SPARC-Auburn/NASA-RMC-2016/Electronics Hardware/Renders/design 3 early sketch.PNG

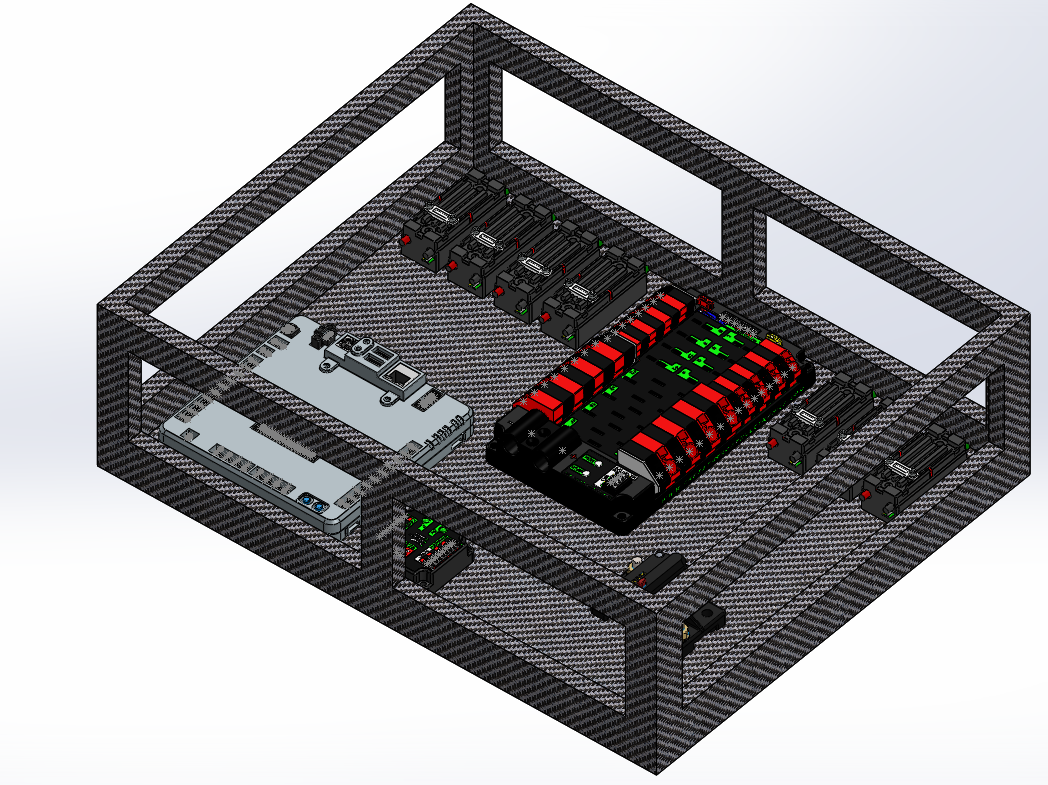
Electronics Hardware/Renders/design 3 early sketch.PNG
