SPARC-Auburn/NASA-RMC-2016/Electronics Hardware/Renders/frame5.PNG

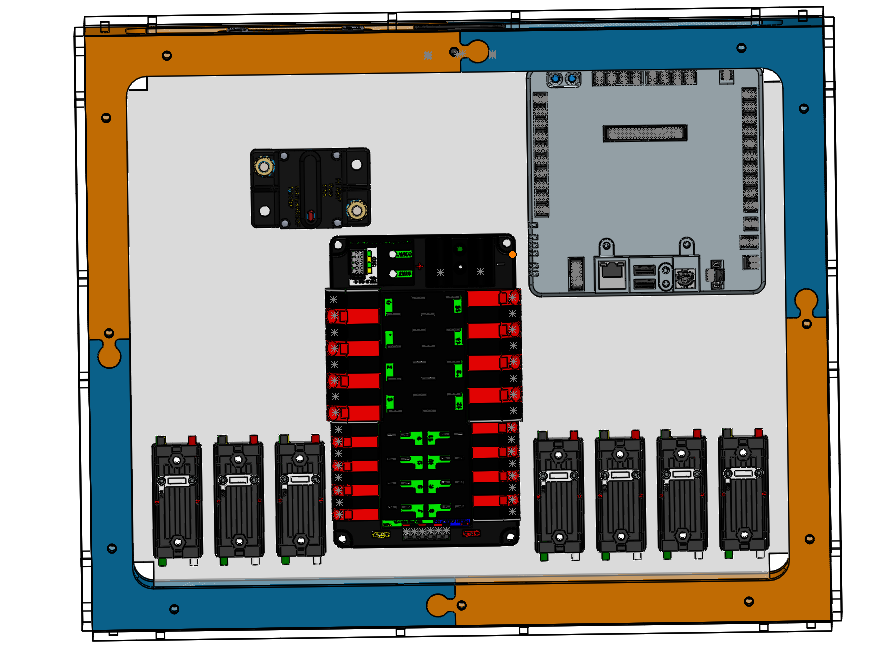
Electronics Hardware/Renders/frame5.PNG
