SPARC-Auburn/NASA-RMC-2016/Electronics Hardware/Renders/snap1.PNG

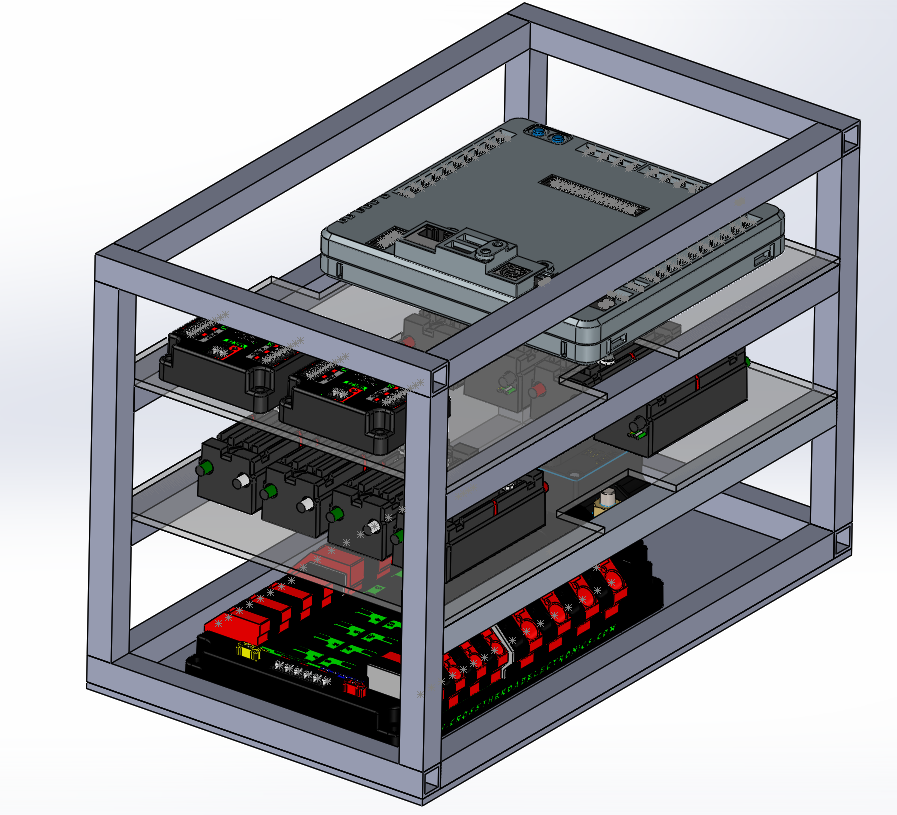
Electronics Hardware/Renders/snap1.PNG
