SPARC-Auburn/NASA-RMC-2016/Electronics Software/Fiducial/spaceclubBlack.png

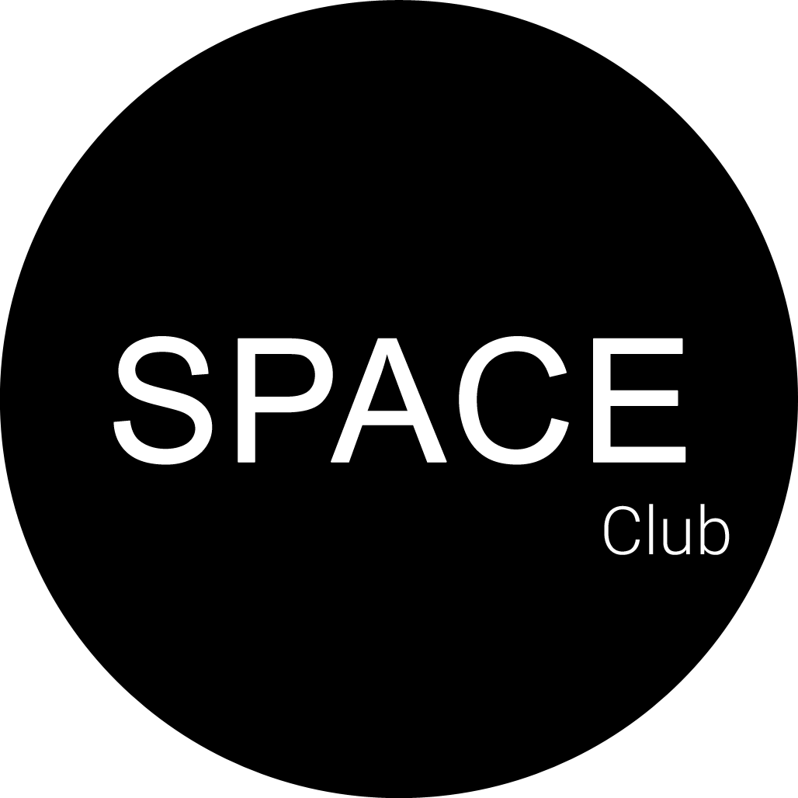
Electronics Software/Fiducial/spaceclubBlack.png
