SPARC-Auburn/NASA-RMC-2016/Electronics Software/Fiducial/sparcABlack.png

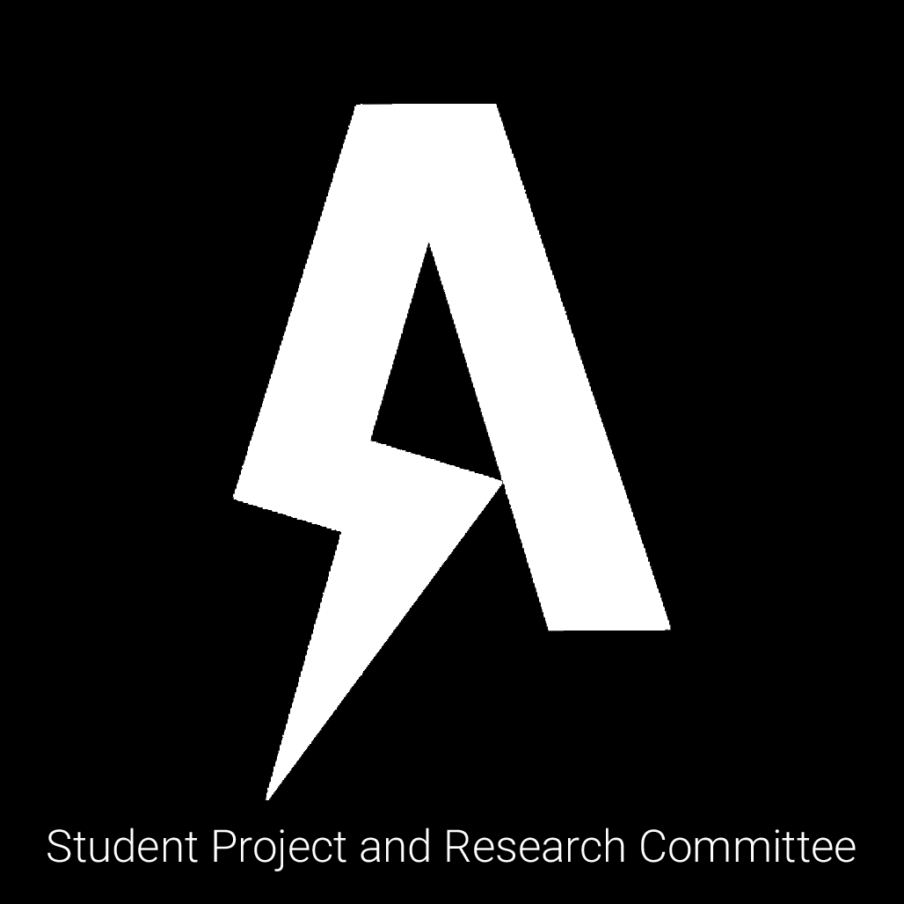
Electronics Software/Fiducial/sparcABlack.png
