SPARC-Auburn/NASA-RMC-2016/Electronics Software/Fiducial/sparcAImpact copy.png

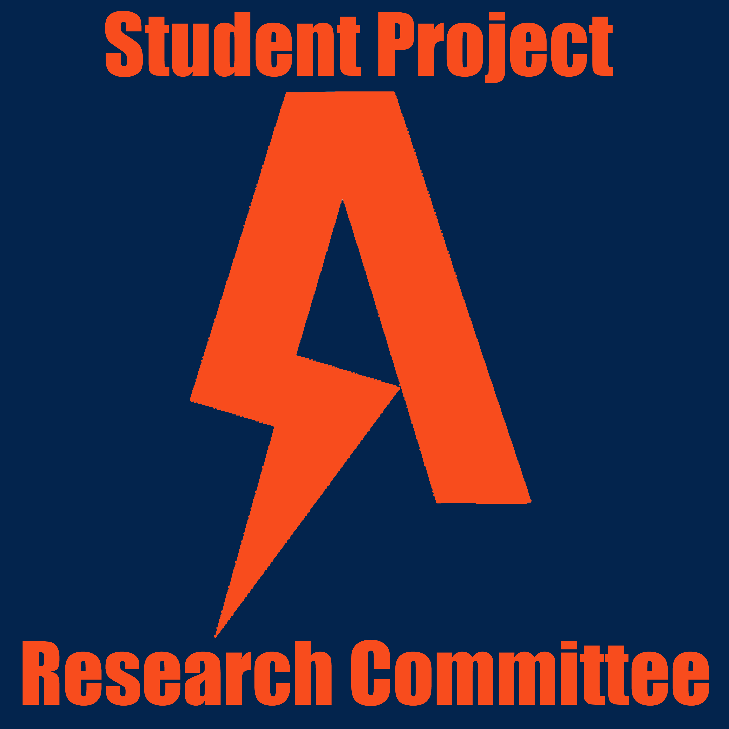
Electronics Software/Fiducial/sparcAImpact copy.png
