SPARC-Auburn/NASA-RMC-2016/Other/T-Shirt/back copy.png

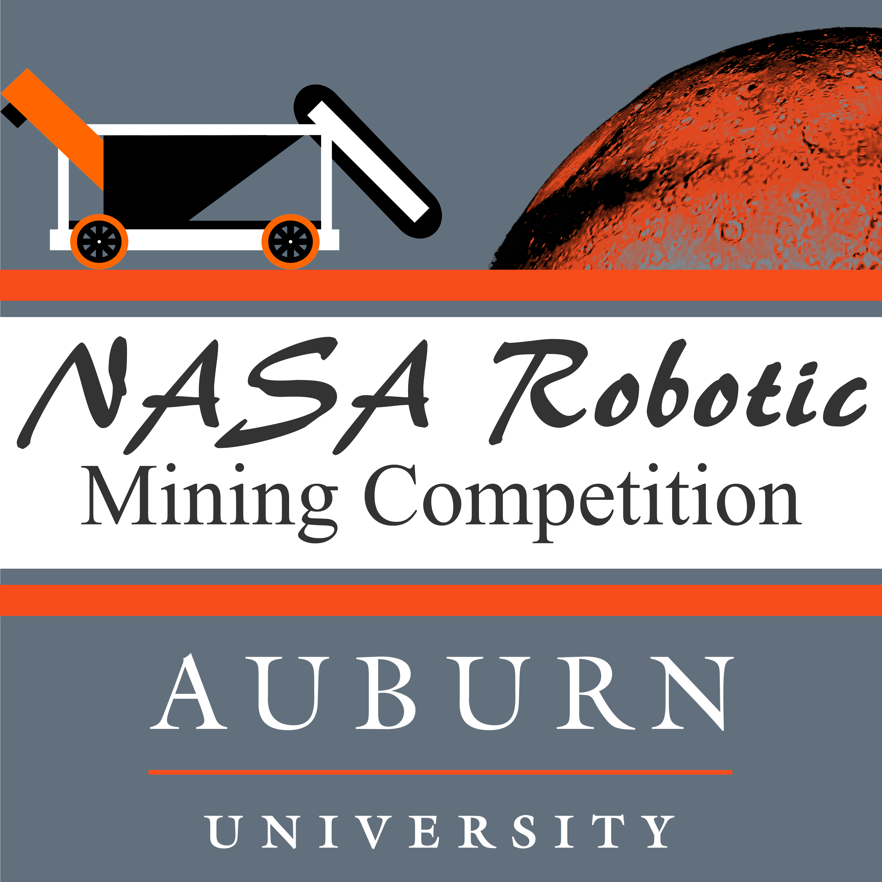
Other/T-Shirt/back copy.png
