SPARC-Auburn/NASA-RMC-2016/Other/T-Shirt/robot.png

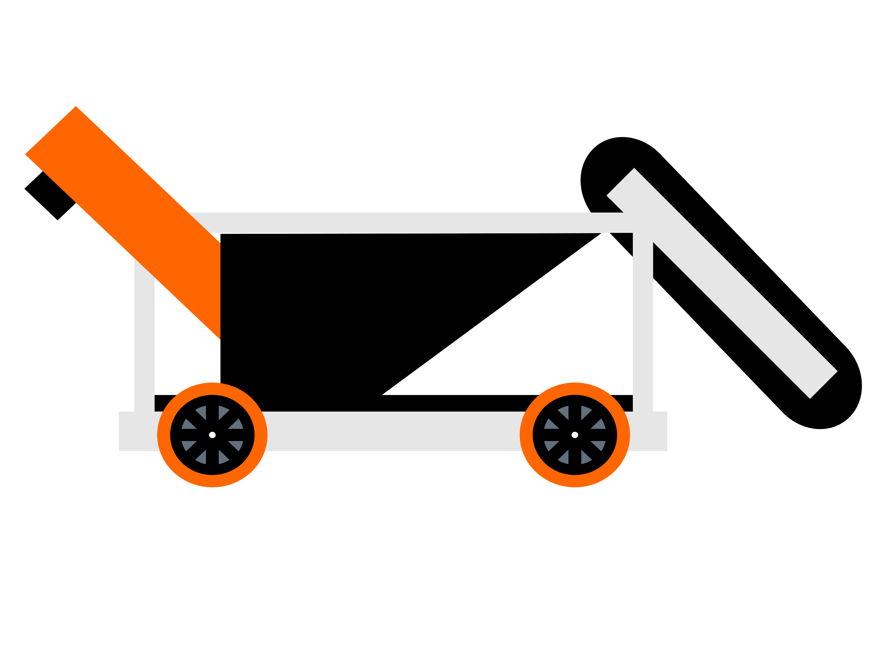
Other/T-Shirt/robot.png
