SPARC-Auburn/NASA-RMC-2016/Electronics Hardware/Final Box CAD/pwrcheck.SLDPRT

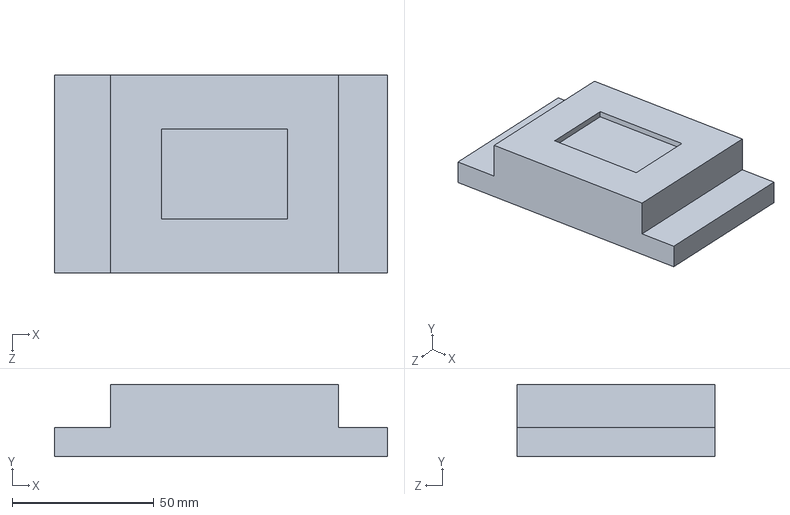
[picture p59: CAD file, 2016-08-08]
Electronics Hardware/Final Box CAD/pwrcheck.SLDPRT
117.5 x 25.4 x 69.8 mm
