SPARC-Auburn/NASA-RMC-2016/Electronics Hardware/Final Box CAD/quarter frame connector.SLDPRT

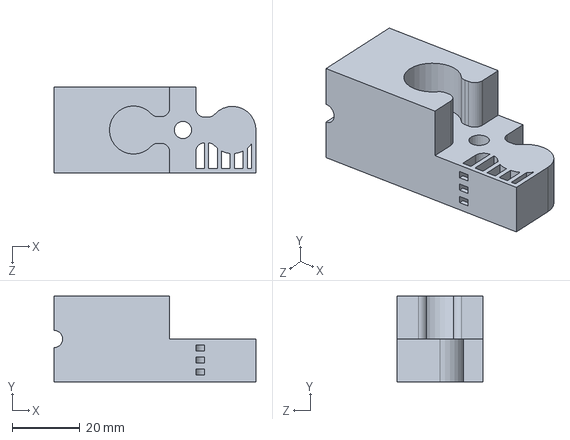
[picture p60: CAD file, 2016-08-08]
Electronics Hardware/Final Box CAD/quarter frame connector.SLDPRT
59.7 x 25.4 x 25.4 mm
