SPARC-Auburn/NASA-RMC-2016/Electronics Hardware/Final Box CAD/Anderson SB50.SLDPRT

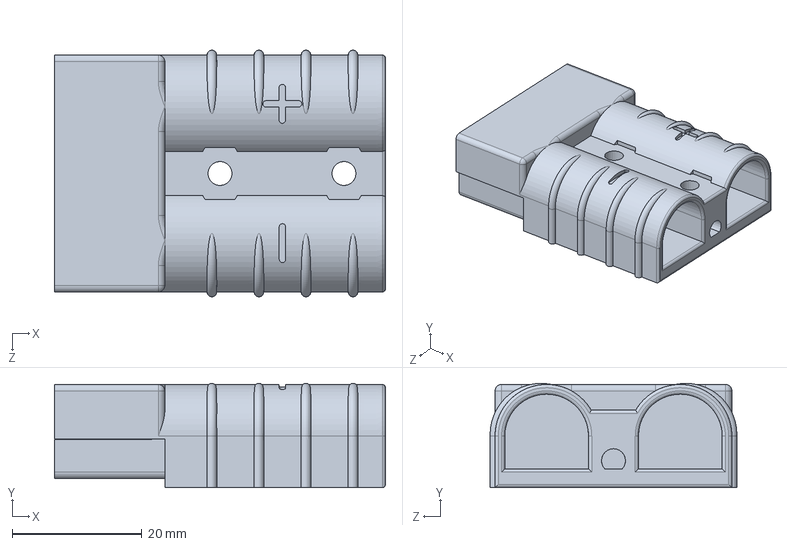
[picture p61: CAD file, 2016-08-08]
Electronics Hardware/Final Box CAD/Anderson SB50.SLDPRT
51.0 x 16.1 x 38.0 mm
