SPARC-Auburn/NASA-RMC-2016/Electronics Hardware/Final Box CAD/powerpole8chassismount.SLDPRT

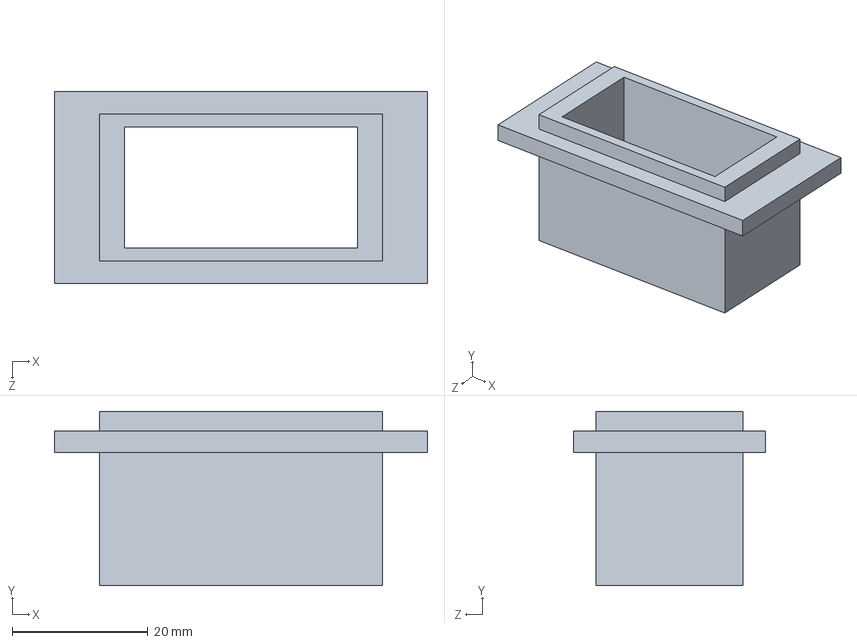
[picture p62: CAD file, 2016-08-08]
Electronics Hardware/Final Box CAD/powerpole8chassismount.SLDPRT
54.9 x 25.7 x 28.2 mm
