SPARC-Auburn/NASA-RMC-2016/Electronics Hardware/Final Box CAD/quarter frame.SLDPRT

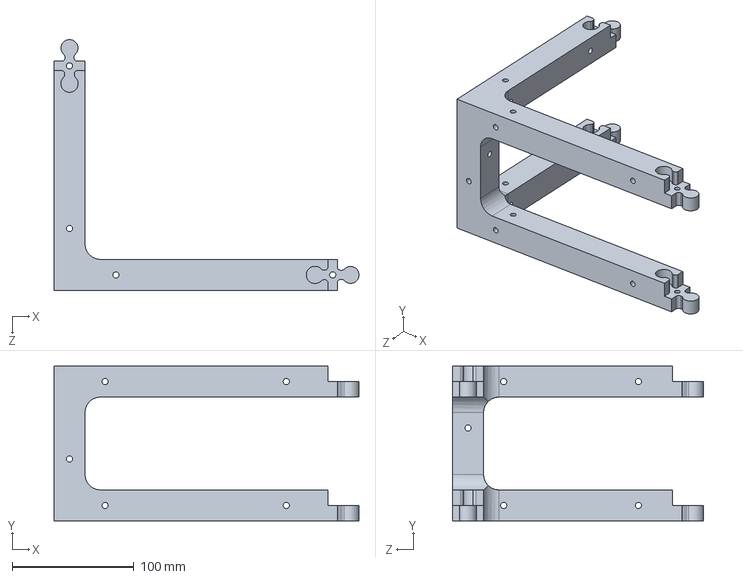
[picture p63: CAD file, 2016-08-08]
Electronics Hardware/Final Box CAD/quarter frame.SLDPRT
250.1 x 127.0 x 205.7 mm
