SPARC-Auburn/NASA-RMC-2016/Electronics Hardware/Final Box CAD/shortplate_left.SLDPRT

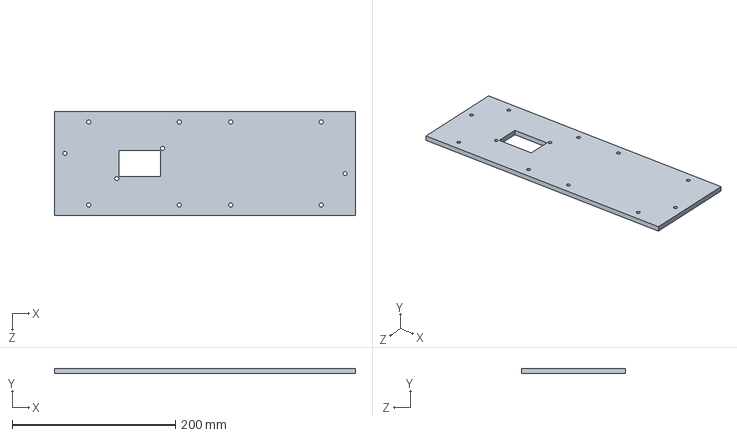
[picture p64: CAD file, 2016-08-08]
Electronics Hardware/Final Box CAD/shortplate_left.SLDPRT
368.3 x 6.35 x 127.0 mm
