SPARC-Auburn/NASA-RMC-2016/Electronics Hardware/Final Box CAD/PowerPoles.SLDPRT

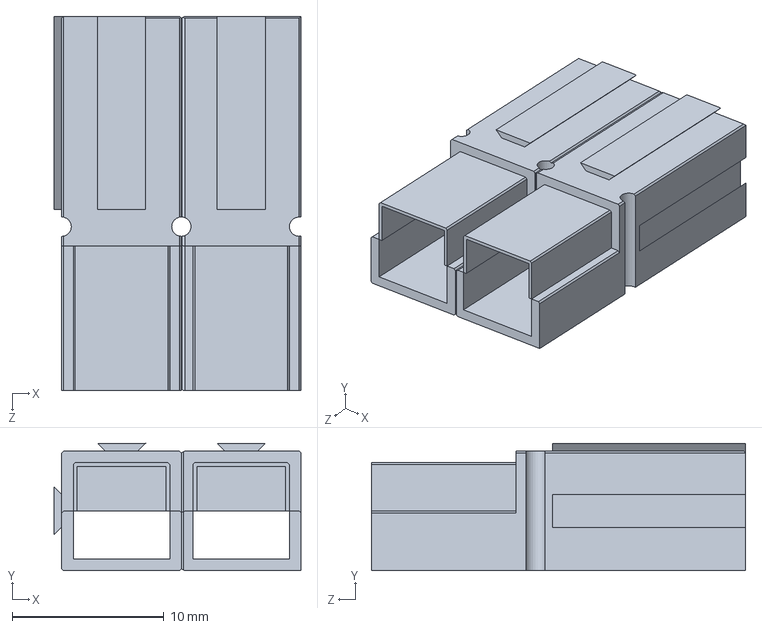
[picture p65: CAD file, 2016-08-08]
Electronics Hardware/Final Box CAD/PowerPoles.SLDPRT
16.3 x 8.38 x 24.6 mm
