SPARC-Auburn/NASA-RMC-2016/Electronics Hardware/Renders/wiring diagram 1.png

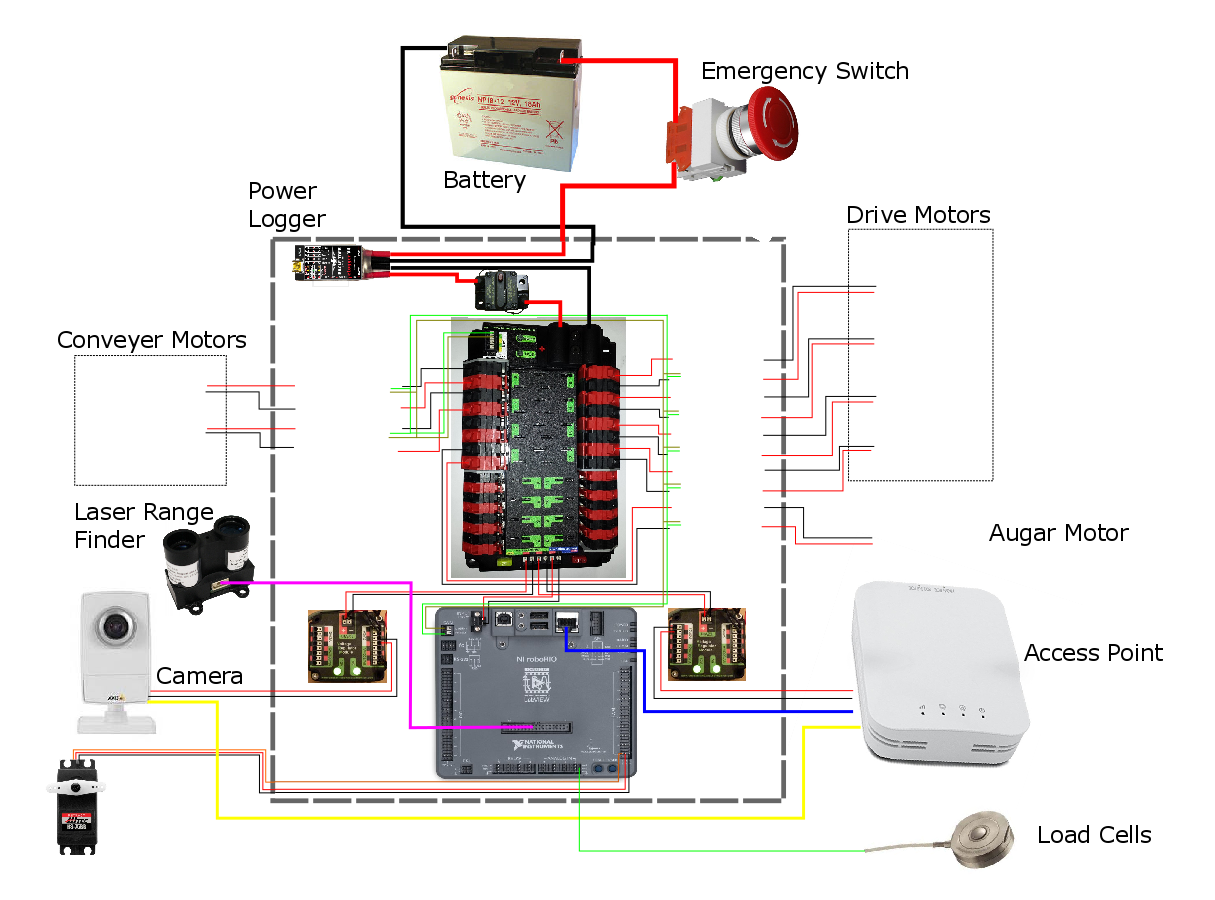
Electronics Hardware/Renders/wiring diagram 1.png
