SPARC-Auburn/NASA-RMC-2016/Electronics Hardware/Renders/wiring diagram.PNG

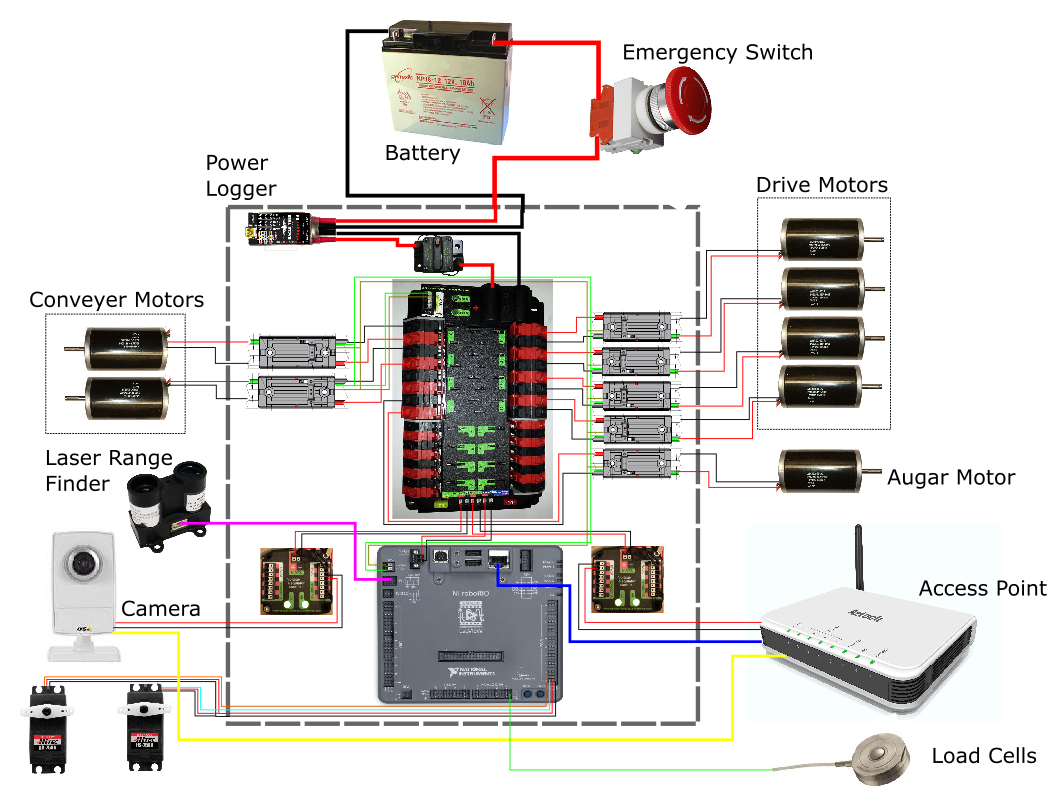
Electronics Hardware/Renders/wiring diagram.PNG
